carcon999/kirakira-ika/source/kiramini/i2s.cpp

/* 
  i2s.c - Software I2S library for esp8266
  
  Code taken and reworked from espessif's I2S example
  
  Copyright (c) 2015 Hristo Gochkov. All rights reserved.
  This file is part of the esp8266 core for Arduino environment.
 
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
  You should have received a copy of the GNU Lesser General Public
  License along with this library; if not, write to the Free Software
  Foundation, Inc., 51 Franklin St, Fifth Floor, Boston, MA  02110-1301  USA
*/
#include "Arduino.h"
#include "osapi.h"
#include "ets_sys.h"
#include "i2s_reg.h"
#include "i2s.h"

#define SLC_BUF_CNT   (2) //Number of buffers in the I2S circular buffer

//We use a queue to keep track of the DMA buffers that are empty. The ISR will push buffers to the back of the queue,
//the mp3 decode will pull them from the front and fill them. For ease, the queue will contain *pointers* to the DMA
//buffers, not the data itself. The queue depth is one smaller than the amount of buffers we have, because there's
//always a buffer that is being used by the DMA subsystem *right now* and we don't want to be able to write to that
//simultaneously.

struct slc_queue_item {
  uint32  blocksize:12;
  uint32  datalen:12;
  uint32  unused:5;
  uint32  sub_sof:1;
  uint32  eof:1;
  uint32  owner:1;
  uint32  buf_ptr;
  uint32  next_link_ptr;
};

static int i2s_buff_length;
static uint32_t i2s_slc_queue[SLC_BUF_CNT-1];
static uint8_t i2s_slc_queue_len;
static uint32_t *i2s_slc_buf_pntr[SLC_BUF_CNT]; //Pointer to the I2S DMA buffer data
static struct slc_queue_item i2s_slc_items[SLC_BUF_CNT]; //I2S DMA buffer descriptors
static uint32_t *i2s_curr_slc_buf=NULL;//current buffer for writing
static int i2s_curr_slc_buf_pos=0; //position in the current buffer

bool ICACHE_FLASH_ATTR i2s_is_full(){
  return (i2s_curr_slc_buf_pos==i2s_buff_length || i2s_curr_slc_buf==NULL) && (i2s_slc_queue_len == 0);
}

bool ICACHE_FLASH_ATTR i2s_is_empty(){
  return (i2s_slc_queue_len >= SLC_BUF_CNT-1);
}

uint32_t ICACHE_FLASH_ATTR i2s_slc_queue_next_item(){ //pop the top off the queue
  uint8_t i;
  uint32_t item = i2s_slc_queue[0];
  i2s_slc_queue_len--;
  for(i=0;i<i2s_slc_queue_len;i++)
    i2s_slc_queue[i] = i2s_slc_queue[i+1];
  return item;
}

//This routine is called as soon as the DMA routine has something to tell us. All we
//handle here is the RX_EOF_INT status, which indicate the DMA has sent a buffer whose
//descriptor has the 'EOF' field set to 1.
void ICACHE_FLASH_ATTR i2s_slc_isr(void) {
  uint32_t slc_intr_status = SLCIS;
  SLCIC = 0xFFFFFFFF;
  if (slc_intr_status & SLCIRXEOF) {
    ETS_SLC_INTR_DISABLE();
    struct slc_queue_item *finished_item = (struct slc_queue_item*)SLCRXEDA;
    memset((void *)finished_item->buf_ptr, 0x00, i2s_buff_length);//zero the buffer so it is mute in case of underflow
    if (i2s_slc_queue_len >= SLC_BUF_CNT-1) { //All buffers are empty. This means we have an underflow
      i2s_slc_queue_next_item(); //free space for finished_item
    }
    i2s_slc_queue[i2s_slc_queue_len++] = finished_item->buf_ptr;
    ETS_SLC_INTR_ENABLE();
  }
}

void ICACHE_FLASH_ATTR i2s_slc_begin(){
  i2s_slc_queue_len = 0;
  int x, y;
  
  for (x=0; x<SLC_BUF_CNT; x++) {
    i2s_slc_buf_pntr[x] = (uint32_t*)malloc(i2s_buff_length);
    for (y=0; y < (i2s_buff_length / sizeof(uint32_t)); y++) i2s_slc_buf_pntr[x][y] = 0;

    i2s_slc_items[x].unused = 0;
    i2s_slc_items[x].owner = 1;
    i2s_slc_items[x].eof = 1;
    i2s_slc_items[x].sub_sof = 0;
    i2s_slc_items[x].datalen = i2s_buff_length;
    i2s_slc_items[x].blocksize = i2s_buff_length;
    i2s_slc_items[x].buf_ptr = (uint32_t)&i2s_slc_buf_pntr[x][0];
    i2s_slc_items[x].next_link_ptr = (int)((x<(SLC_BUF_CNT-1))?(&i2s_slc_items[x+1]):(&i2s_slc_items[0]));
  }

  ETS_SLC_INTR_DISABLE();
  SLCC0 |= SLCRXLR | SLCTXLR;
  SLCC0 &= ~(SLCRXLR | SLCTXLR);
  SLCIC = 0xFFFFFFFF;

  //Configure DMA
  SLCC0 &= ~(SLCMM << SLCM); //clear DMA MODE
  SLCC0 |= (1 << SLCM); //set DMA MODE to 1
  SLCRXDC |= SLCBINR | SLCBTNR; //enable INFOR_NO_REPLACE and TOKEN_NO_REPLACE
  SLCRXDC &= ~(SLCBRXFE | SLCBRXEM | SLCBRXFM); //disable RX_FILL, RX_EOF_MODE and RX_FILL_MODE

  //Feed DMA the 1st buffer desc addr
  //To send data to the I2S subsystem, counter-intuitively we use the RXLINK part, not the TXLINK as you might
  //expect. The TXLINK part still needs a valid DMA descriptor, even if it's unused: the DMA engine will throw
  //an error at us otherwise. Just feed it any random descriptor.
  SLCTXL &= ~(SLCTXLAM << SLCTXLA); // clear TX descriptor address
  SLCTXL |= (uint32)&i2s_slc_items[1] << SLCTXLA; //set TX descriptor address. any random desc is OK, we don't use TX but it needs to be valid
  SLCRXL &= ~(SLCRXLAM << SLCRXLA); // clear RX descriptor address
  SLCRXL |= (uint32)&i2s_slc_items[0] << SLCRXLA; //set RX descriptor address

  ETS_SLC_INTR_ATTACH(i2s_slc_isr, NULL);
  SLCIE = SLCIRXEOF; //Enable only for RX EOF interrupt

  ETS_SLC_INTR_ENABLE();

  //Start transmission
  SLCTXL |= SLCTXLS;
  SLCRXL |= SLCRXLS;
}

void ICACHE_FLASH_ATTR i2s_slc_end(){
  ETS_SLC_INTR_DISABLE();
  SLCIC = 0xFFFFFFFF;
  SLCIE = 0;
  SLCTXL &= ~(SLCTXLAM << SLCTXLA); // clear TX descriptor address
  SLCRXL &= ~(SLCRXLAM << SLCRXLA); // clear RX descriptor address

  for (int x = 0; x<SLC_BUF_CNT; x++) {
	  free(i2s_slc_buf_pntr[x]);
  }
}

//This routine pushes a single, 32-bit sample to the I2S buffers. Call this at (on average) 
//at least the current sample rate. You can also call it quicker: it will suspend the calling
//thread if the buffer is full and resume when there's room again.

bool ICACHE_FLASH_ATTR i2s_write(uint32_t* pbuff){
  if (i2s_curr_slc_buf_pos==i2s_buff_length || i2s_curr_slc_buf==NULL) {
    if(i2s_slc_queue_len == 0){
      return false;
    }
    ETS_SLC_INTR_DISABLE();
    i2s_curr_slc_buf = (uint32_t *)i2s_slc_queue_next_item();
    ETS_SLC_INTR_ENABLE();
    i2s_curr_slc_buf_pos=0;
  }
  memcpy(i2s_curr_slc_buf, pbuff, i2s_buff_length);
  i2s_curr_slc_buf_pos = i2s_buff_length;
  return true;
}

//  END DMA
// =========
// START I2S


static uint32_t _i2s_sample_rate;

void ICACHE_FLASH_ATTR i2s_set_rate(uint32_t rate){ //Rate in HZ
  if(rate == _i2s_sample_rate) return;
  _i2s_sample_rate = rate;
  uint32_t i2s_clock_div = (I2SBASEFREQ/(_i2s_sample_rate*32)) & I2SCDM;
  uint8_t i2s_bck_div = (I2SBASEFREQ/(_i2s_sample_rate*i2s_clock_div*2)) & I2SBDM;
  //os_printf("Rate %u Div %u Bck %u Frq %u\n", _i2s_sample_rate, i2s_clock_div, i2s_bck_div, I2SBASEFREQ/(i2s_clock_div*i2s_bck_div*2));

  //!trans master, !bits mod, rece slave mod, rece msb shift, right first, msb right
  I2SC &= ~(I2STSM | (I2SBMM << I2SBM) | (I2SBDM << I2SBD) | (I2SCDM << I2SCD));
  I2SC |= I2SRF | I2SMR | I2SRSM | I2SRMS | ((i2s_bck_div-1) << I2SBD) | ((i2s_clock_div-1) << I2SCD);
}

void ICACHE_FLASH_ATTR i2s_begin(uint32_t sz){

  i2s_buff_length = sz;    // len * RGB * bitflag
  _i2s_sample_rate = 0;
  i2s_slc_begin();

// not use LRCK and SCLK
//  pinMode(2, FUNCTION_1); //I2SO_WS (LRCK)
  pinMode(3, FUNCTION_1); //I2SO_DATA (SDIN)
//  pinMode(15, FUNCTION_1); //I2SO_BCK (SCLK)    // pin6
  
//  I2S_CLK_ENABLE();
  I2SIC = 0x3F;
  I2SIE = 0;
  
  //Reset I2S
  I2SC &= ~(I2SRST);
  I2SC |= I2SRST;
  I2SC &= ~(I2SRST);
  
  I2SFC &= ~(I2SDE | (I2STXFMM << I2STXFM) | (I2SRXFMM << I2SRXFM)); //Set RX/TX FIFO_MOD=0 and disable DMA (FIFO only)
  I2SFC |= I2SDE; //Enable DMA
  I2SCC &= ~((I2STXCMM << I2STXCM) | (I2SRXCMM << I2SRXCM)); //Set RX/TX CHAN_MOD=0
  i2s_set_rate(44100);
  I2SC |= I2STXS; //Start transmission
}

void ICACHE_FLASH_ATTR i2s_end(){
  I2SC &= ~I2STXS;

  //Reset I2S
  I2SC &= ~(I2SRST);
  I2SC |= I2SRST;
  I2SC &= ~(I2SRST);

// not use LRCK and SCLK
//  pinMode(2, INPUT);
  pinMode(3, INPUT);
//  pinMode(15, INPUT);

  i2s_slc_end();
}
